veis-lzf/CameraCapture/software/drivers/inc/drivers.h

#ifndef _DRIVERS_H
#define _DRIVERS_H

#include "bsp.h"
#include "driver_misc.h"
#include "hard_timer.h"
#include "rtc.h"
#include "iwdg.h"
#include "bsp_exti.h"
#include "bsp_uart.h"
#include "bsp_ov2640.h"
#include "bsp_dcmi.h"
#include "bsp_pwm.h"
#include "bsp_led.h"
#include "bsp_sdio_sd.h"

#ifdef SURPPORT_USB
#include "usbh_ioreq.h"
#include "usbh_hcs.h"
#include "usbh_usr.h"
#endif
#endif
