veis-lzf/CameraCapture/software/drivers/inc/bsp_ov2640cfg.h

#ifndef _OV2640CFG_H
#define _OV2640CFG_H

#include "bsp_ov2640.h"
//OV2640 SXGA初始化寄存器序列表
//此模式下帧率为15帧
//SXGA(1600*1200) 
const uint8_t ov2640_sxga_init_reg_tbl[][2]= 
{   
	0xff, 0x00,
	0x2c, 0xff,
	0x2e, 0xdf,
	0xff, 0x01,
	0x3c, 0x32,
	//
	0x11, 0x00,
	0x09, 0x02,
	0x04, 0xD8,//水平镜像,垂直翻转
	0x13, 0xe5,
	0x14, 0x48,
	0x2c, 0x0c,
	0x33, 0x78,
	0x3a, 0x33,
	0x3b, 0xfB,
	//
	0x3e, 0x00,
	0x43, 0x11,
	0x16, 0x10,
	//
	0x39, 0x92,
	//
	0x35, 0xda,
	0x22, 0x1a,
	0x37, 0xc3,
	0x23, 0x00,
	0x34, 0xc0,
	0x36, 0x1a,
	0x06, 0x88,
	0x07, 0xc0,
	0x0d, 0x87,
	0x0e, 0x41,
	0x4c, 0x00,
	
	0x48, 0x00,
	0x5B, 0x00,
	0x42, 0x03,
	//
	0x4a, 0x81,
	0x21, 0x99,
	//
	0x24, 0x40,
	0x25, 0x38,
	0x26, 0x82,
	0x5c, 0x00,
	0x63, 0x00,
	0x46, 0x00,
	0x0c, 0x3c,
	//
	0x61, 0x70,
	0x62, 0x80,
	0x7c, 0x05,
	//
	0x20, 0x80,
	0x28, 0x30,
	0x6c, 0x00,
	0x6d, 0x80,
	0x6e, 0x00,
	0x70, 0x02,
	0x71, 0x94,
	0x73, 0xc1, 
	0x3d, 0x34, 
	0x5a, 0x57,
	//
	0x12, 0x00,//UXGA 1600*1200
	
	0x17, 0x11,
	0x18, 0x75,
	0x19, 0x01,
	0x1a, 0x97,
	0x32, 0x36,
	0x03, 0x0f, 
	0x37, 0x40,
	// 
	0x4f, 0xca,
	0x50, 0xa8,
	0x5a, 0x23,
	0x6d, 0x00,
	0x6d, 0x38,
	//
	0xff, 0x00,
	0xe5, 0x7f,
	0xf9, 0xc0,
	0x41, 0x24,
	0xe0, 0x14,
	0x76, 0xff,
	0x33, 0xa0,
	0x42, 0x20,
	0x43, 0x18,
	0x4c, 0x00,
	0x87, 0xd5,
	0x88, 0x3f,
	0xd7, 0x03,
	0xd9, 0x10,
	0xd3, 0x82,
	//
	0xc8, 0x08,
	0xc9, 0x80,
	//
	0x7c, 0x00,
	0x7d, 0x00,
	0x7c, 0x03,
	0x7d, 0x48,
	0x7d, 0x48,
	0x7c, 0x08,
	0x7d, 0x20,
	0x7d, 0x10,
	0x7d, 0x0e,
	//
	0x90, 0x00,
	0x91, 0x0e,
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
{
	0xFF, 0x00,
	0xDA, 0x09,
	0xD7, 0x03,
	0xDF, 0x02,
	0x33, 0xa0,
	0x3C, 0x00,
	0xe1, 0x67,
	
	0xff, 0x01, 
	0xe0, 0x00,
	0xe1, 0x00,
	0xe5, 0x00,
	0xd7, 0x00, 
	0xda, 0x00,
	0xe0, 0x00,  
};
const uint8_t ov2640_yuv422_reg_tbl[][2]= 
{
	0xFF, 0x00, 
	0xDA, 0x10,
	0xD7, 0x03,
	0xDF, 0x00,
	0x33, 0x80,
	0x3C, 0x40,
	0xe1, 0x77,
	0x00, 0x00,
};

#endif
