veis-lzf/CameraCapture/software/usrApp/debug.c

#include "debug.h"
#include "bsp_uart.h"
#include "protocol.h"
#include <string.h>
#include <stdio.h>

#define LOWPWR_CMD	101
#define ENTER_LWP	0x01

uint8_t DataRxBuffer[RX_BUF_MAX_LEN] = {0};
uint8_t dbg_rxdata = 0;
static uint32_t count = 0;

// debug串口接收记录集
STRUCT_USARTx_Fram dbg_Fram_Record = 
{
	DataRxBuffer,
	0
};

// 调试等级
int dbg_level = Monitor;
extern uint8_t *pname;
static int OnCfgDebug(uint32_t vp_Type, uint32_t vp_P1, uint32_t vp_P2, uint32_t vp_P3)
{
	p_info("info:OnCfgDebug:Type=%d,P1=%d,P2=%d,P3=%d.", vp_Type, vp_P1, vp_P2, vp_P3);
	
	switch(vp_Type)
	{
	case ENTER_LWP:
	{
		Set_PWM_Value(PWM1, vp_P1);
		break;
	}
	case 2:
	{
		if(SDCARD_Status == SD_CARD_STATUS_OK)	// SD卡就绪
		{  
			camera_new_pathname(pname, 1);//得到文件名
			p_info("name:%s", pname);
			if(take_jpg_photo(pname))
			{
				p_info("take photo failed!");
			}
			else
			{
				p_info("take photo successful!");
			}
			jpeg_data_ok = PROCESS_COMPLETE;           
		}
		break;
	}
	
	case 3:
	{
		_uart_PhotoOk();
		break;
	}
	
	case 4:
	{
		_uart_PhotoError();
		break;
	}
	default:
		p_info("warn:PARAM INVALID!");
		break;
	}
	memset(DataRxBuffer, 0, RX_BUF_MAX_LEN);
	return 0;
}

// 格式：AT+cmdCfg=vl_CmdId,vl_Type,vl_P1,vl_P2,vl_P3
// 设置定时器命令：666
// 设置关闭和开始时间类型：1
// 开启时间和关闭时间：vl_P1，vl_P2
static int AT_DeviceHandle(const unsigned char *data_buf)
{
	count = 0;
	
	uint32_t i, vl_CmdId, vl_Type, vl_P1, vl_P2, vl_P3;
	uint32_t nlen = strlen((const char *)data_buf);
	char vl_FormateStr[64];
	
	vl_CmdId = 0;
	vl_Type = 0;
	vl_P1 = 0;
	vl_P2 = 0;
	vl_P3 = 0;
	
	p_dbg("data_buf=%s", data_buf);
	if(!strstr((const char *)data_buf, "="))
		goto RETURN;

	memset(vl_FormateStr, 0, sizeof(vl_FormateStr)/sizeof(vl_FormateStr[0]));
	memcpy(vl_FormateStr, "AT+cmdCfg=%d", strlen("AT+cmdCfg=%d"));
	
	p_dbg("nlen=%d", nlen);
	for (i = 0; i < nlen; i++)
	{
		if ((',' == data_buf[i]) && (i < nlen - 1))
			memcpy(vl_FormateStr + strlen(vl_FormateStr), ",%d", strlen(",%d"));
	}
	p_dbg("vl_FormateStr=%s", vl_FormateStr);
	sscanf((const char *)data_buf, vl_FormateStr, &vl_CmdId, 
		&vl_Type, &vl_P1, &vl_P2, &vl_P3);
	
	memset((char *)data_buf, 0, nlen);
	
	p_dbg("vl_CmdId=%d, vl_Type=%d, vl_P1=%d, vl_P2=%d, vl_P3=%d", vl_CmdId, vl_Type, vl_P1, vl_P2, vl_P3);
	
	if (LOWPWR_CMD == vl_CmdId)
		return OnCfgDebug(vl_Type, vl_P1, vl_P2, vl_P3);

RETURN:
	return -1;
}


/**
 * @brief      获取系统时间基准
 *
 * @return     返回系统CPU运行时间
 */
uint32_t os_time_get(void)
{
	return RTC_GetTraceTick();
}

/**
 * @brief      串口接收回调函数
 *
 * @param      串口实例
 */
void UART_RxCpltCallback(USART_TypeDef* USARTx)
{
	if(USARTx == USART1)
	{
		dbg_rxdata = USART1->DR;
		//putchar(dbg_rxdata);
		if(dbg_rxdata != 0x0d && dbg_rxdata != 0x0a)
		{
			DataRxBuffer[count++] = dbg_rxdata;
		}
		else if(dbg_rxdata != 0x0a)
		{
			DataRxBuffer[count] = '\0';
			AT_DeviceHandle(DataRxBuffer); // 调用解析接口函数
		}
	}
	else if(USARTx == USART3)
	{
		Receive_Handle(ack_buffer, ack_len);
	//	usart1_sendArray(ack_buffer, ack_len);
	}
}

/**
 * @brief      重写fputc
 *
 * @param[in]  ch    待发送参数
 * @param      f     设备文件
 *
 * @return     返回发送的字符
 */

//IAR9不能使用fputc，要改用putchar
int fputc(int ch, FILE *file)
{
    while((USART1->SR&0X40)==0);
    USART1->DR = (uint8_t)ch;
	return (ch);
}
