veis-lzf/CameraCapture/software/drivers/inc/app.h

#ifndef __APP_H__
#define __APP_H__

//#include "debug.h"
#include "app_cfg.h"
#include "sys_misc.h"
#include "driver_misc.h"
#include "diskio.h"
#include "photo.h"
#include "jx_uart_send.h"

extern uint8_t SDCARD_Status;	//0,sd卡不正常;1,SD卡正常. 

#endif
