veis-lzf/CameraCapture/software/drivers/inc/bsp_led.h

#ifndef __BSP_LED_H__
#define __BSP_LED_H__

#include "drivers.h"

typedef enum
{
	LED1 = 0,
	LED2,
	
	LED_NULL,
} eLED_CHANNEL;

typedef enum
{
	LED_OFF,
	LED_ON,
	LED_MODE1_ON,
	LED_MODE2_ON,
	LED_MODE3_ON,
} eLED_Status;

void LED_Init(void);
void Set_LED_Status(eLED_CHANNEL channel, eLED_Status status);

#endif
