veis-lzf/CameraCapture/software/drivers/inc/bsp_sccb.h

#ifndef _SSCB_H
#define _SSCB_H

#include "bsp.h"


#define SCCB_ID 0X60 // OV2640µÄID

///////////////////////////////////////////
void SCCB_Init(void);
void SCCB_Start(void);
void SCCB_Stop(void);
void SCCB_No_Ack(void);
uint8_t SCCB_WR_Byte(uint8_t dat);
uint8_t SCCB_RD_Byte(void);
uint8_t SCCB_WR_Reg(uint8_t reg,uint8_t data);
uint8_t SCCB_RD_Reg(uint8_t reg);

#endif
